paulc/c3zero-doorbell/src/ws2812_quad.rs

use anyhow::Result;
use esp_idf_hal::rmt::{config::TransmitConfig, FixedLengthSignal, PinState, Pulse, TxRmtDriver};
use std::time::Duration;

use crate::rgb::{Rgb, RgbLayout};

// ws2812 timings
const T0H: u64 = 400;
const T0L: u64 = 850;
const T1H: u64 = 800;
const T1L: u64 = 450;
const _RESET: u64 = 50000;

pub type Ws2812RmtChannel = esp_idf_hal::rmt::CHANNEL0;

// Quad WS2812 status display on RMT Channel 0
pub struct Ws2812RmtQuad<'a> {
    tx: TxRmtDriver<'a>,
    format: RgbLayout,
}

impl Ws2812RmtQuad<'_> {
    pub fn new(
        led: esp_idf_hal::gpio::AnyOutputPin,
        channel: Ws2812RmtChannel,
        format: RgbLayout,
    ) -> Result<Self> {
        let config = TransmitConfig::new().clock_divider(1);
        let tx = TxRmtDriver::new(channel, led, &config)?;
        Ok(Self { tx, format })
    }

    pub fn set(&mut self, leds: &[Rgb; 4]) -> Result<()> {
        let ticks_hz = self.tx.counter_clock()?;
        let (t0h, t0l, t1h, t1l) = (
            Pulse::new_with_duration(ticks_hz, PinState::High, &Duration::from_nanos(T0H))?,
            Pulse::new_with_duration(ticks_hz, PinState::Low, &Duration::from_nanos(T0L))?,
            Pulse::new_with_duration(ticks_hz, PinState::High, &Duration::from_nanos(T1H))?,
            Pulse::new_with_duration(ticks_hz, PinState::Low, &Duration::from_nanos(T1L))?,
        );
        let mut signal = FixedLengthSignal::<96>::new();
        for (n, led) in leds.iter().enumerate() {
            let colour: u32 = led.to_u32(self.format);
            for i in (0..24).rev() {
                if (colour >> i) & 1 == 0 {
                    signal.set((n * 24) + 23 - i, &(t0h, t0l))?;
                } else {
                    signal.set((n * 24) + 23 - i, &(t1h, t1l))?;
                }
            }
        }
        self.tx.start_blocking(&signal)?;
        Ok(())
    }
}
