paulc/c3zero-doorbell/examples/doorbell/main.rs

#![feature(lock_value_accessors)]

use esp_idf_hal::gpio::OutputPin;
use esp_idf_svc::eventloop::EspSystemEventLoop;
use esp_idf_svc::hal::prelude::*;
use esp_idf_svc::http::Method;
use esp_idf_svc::nvs::EspDefaultNvsPartition;
use esp_idf_svc::wifi::EspWifi;

use std::sync::{mpsc, Mutex};
use std::thread;
use std::time::Duration;

use doorbell::nvs::NVStore;
use doorbell::ota::Ota;
use doorbell::web::{BuildInfo, HomePage, NavBar, NavLink, WebServer};
use doorbell::wifi::{APConfig, APStore, WifiManager, WifiState};
use doorbell::ws2812::{colour, RgbLayout, Ws2812RmtSingle};

mod adc;
mod errlog;
mod led_task;
mod mqtt;
mod pushover;
mod watchdog;

const AP_SSID: &str = "ESP32C3-AP";
const AP_PASSWORD: &str = "password";

const NVS_NAMESPACE: &str = "DOORBELL";

const WATCHDOG_TIMEOUT: u64 = 60;

const BUILD_INFO: BuildInfo = BuildInfo {
    build_ts: env!("BUILD_TS"),
    build_branch: env!("BUILD_BRANCH"),
    build_hash: env!("BUILD_HASH"),
    build_profile: env!("BUILD_PROFILE"),
};

pub static WIFI_STATE: Mutex<WifiState> = Mutex::new(WifiState::NotConnected);

// Static NavBar
pub const NAVBAR: NavBar = NavBar {
    title: "Doorbell",
    links: &[
        NavLink {
            url: "/wifi",
            label: "Wifi",
        },
        NavLink {
            url: "/mqtt",
            label: "MQTT",
        },
        NavLink {
            url: "/pushover",
            label: "Pushover",
        },
        NavLink {
            url: "/ota_page",
            label: "OTA",
        },
        NavLink {
            url: "/adc",
            label: "ADC",
        },
        NavLink {
            url: "/reset_page",
            label: "Reset",
        },
    ],
};

fn main() -> anyhow::Result<()> {
    // It is necessary to call this function once. Otherwise some patches to the runtime
    // implemented by esp-idf-sys might not link properly. See https://github.com/esp-rs/esp-idf-template/issues/71
    esp_idf_svc::sys::link_patches();

    // Bind the log crate to the ESP Logging facilities
    esp_idf_svc::log::EspLogger::initialize_default();
    log::info!("Starting...");

    // Initialise peripherals
    let peripherals = Peripherals::take()?;
    let sys_loop = EspSystemEventLoop::take()?;
    let nvs_default_partition = EspDefaultNvsPartition::take()?;

    // Hardware Watchdog
    watchdog::init(peripherals.twdt, Duration::from_secs(WATCHDOG_TIMEOUT))?;

    // NVStore
    let nvs = NVStore::init(nvs_default_partition.clone(), NVS_NAMESPACE)?;

    // WiFi
    let mut wifi = WifiManager::new(EspWifi::new(
        peripherals.modem,
        sys_loop.clone(),
        Some(nvs_default_partition.clone()),
    )?)?;

    // Onboard WS2812 (GPIO10)
    let ws2812 = peripherals.pins.gpio10.downgrade_output();
    let channel = peripherals.rmt.channel0;
    let mut led = Ws2812RmtSingle::new(ws2812, channel, RgbLayout::Grb)?;
    led.set(colour::OFF)?;

    // LED task
    let (led_tx, led_rx) = mpsc::channel::<led_task::LedMessage>();
    let _led_task_id = thread::spawn(move || led_task::led_task(led, led_rx));

    // Start web server
    let mut web = WebServer::new(NAVBAR)?;

    // OTA
    let ota = Ota::new();

    // Add module handlers
    nvs.add_handlers(&mut web, NAVBAR)?;
    wifi.add_handlers(&mut web, NAVBAR)?;
    ota.add_handlers(&mut web, NAVBAR)?;

    // Home Page
    let home_page = HomePage::new(NAVBAR.title, BUILD_INFO.display_fields(), NAVBAR);
    home_page.set_status(WIFI_STATE.get_cloned()?.display_fields())?;
    web.add_handler("/", Method::Get, home_page.make_handler())?;

    // ADC Task
    let (adc_tx, adc_rx) = mpsc::channel();

    let _adc_task_id = adc::adc_task(
        peripherals.timer00,
        peripherals.adc1,
        peripherals.pins.gpio4,
        adc_tx,
    )?;

    web.add_handler("/adc/debug/on", Method::Get, adc::adc_debug_on_handler)?;
    web.add_handler("/adc/debug/off", Method::Get, adc::adc_debug_off_handler)?;
    web.add_handler("/adc/data", Method::Get, adc::adc_data)?;
    web.add_handler("/adc/set_params", Method::Post, adc::adc_set_params)?;
    web.add_handler("/adc", Method::Get, adc::make_adc_page(NAVBAR))?;

    // MQTT
    let mqtt_task = mqtt::MqttTask::new()?;
    mqtt_task.add_handlers(&mut web, NAVBAR)?;

    // Pushover
    let mut pushover = pushover::PushoverSender::new()?;
    pushover.add_handlers(&mut web, NAVBAR)?;

    // Start watchdog after initialisation
    watchdog::subscribe()?;
    let mut count = 0_usize;

    loop {
        let wifi_state = WIFI_STATE.get_cloned()?;
        let wifi_connected = wifi.is_connected()?;

        if !wifi_connected {
            log::info!("{wifi_state} :: {wifi_connected}");
        }

        match (&wifi_state, wifi_connected) {
            (WifiState::NotConnected, _) => {
                // NotConnected - try to connect to known AP (or start local AP)
                led_tx.send(led_task::LedMessage::Flash(colour::GREEN))?;
                wifi.scan()?;
                let wifi_state = wifi.try_connect(
                    &APStore::get_aps()?,
                    Some(APConfig::new(AP_SSID, AP_PASSWORD)?),
                    30_000,
                )?;
                log::info!("WifiState: {wifi_state:?}");

                // If we have connected start services
                if let WifiState::Station(_, _) = wifi_state {
                    // Start services
                    log::info!("Starting mqtt_task:");
                    mqtt_task.run()?;
                    mqtt_task.ring_msg(false)?;
                }

                // Update home page status
                home_page.set_status(wifi_state.display_fields())?;

                // Update WIFI_STATE
                WIFI_STATE.replace(wifi_state)?;

                // Update watchdog
                watchdog::feed()?;
            }
            (WifiState::Station(ref ap, _), false) => {
                log::error!("{count} :: {wifi_state} :: {wifi_connected}");
                // WiFi disconnected - try to reconnect (every 5 secs)
                if count.is_multiple_of(5) {
                    log::error!("WIFi Disconnected: Attempting to reconnect");
                    match wifi.connect_sta(ap, 30_000) {
                        Ok(WifiState::Station(config, ip_info)) => {
                            let wifi_state = WifiState::Station(config, ip_info);
                            log::info!("WIFi Reconnected: {wifi_state}");
                            // Update home page status
                            home_page.set_status(wifi_state.display_fields())?;
                            // Update WIFI_STATE
                            WIFI_STATE.replace(wifi_state)?;
                        }
                        Ok(_) => {
                            log::info!("WiFi Failed to Reconnect");
                        }
                        Err(e) => {
                            // Something went wrong - possibly reboot?
                            log::info!("WiFi Error Reconnecting: {e}");
                        }
                    }
                }

                // Flush adc_rx buffer
                while adc_rx.try_recv().is_ok() {}
                led_tx.send(led_task::LedMessage::Flash(colour::WHITE))?;
                thread::sleep(Duration::from_millis(1000));

                // We dont update watchdog here - timeout and reset if we dont re-connect
            }
            (WifiState::Station(_, _), true) => {
                // WiFi Online
                match adc_rx.recv_timeout(Duration::from_millis(1000)) {
                    Ok(msg) => match msg {
                        adc::RingMessage::RingStart(ref _s) => {
                            log::info!("adc_rx :: {msg:?}");
                            if let Err(e) = led_tx.send(led_task::LedMessage::Ring(true)) {
                                log::error!("LED Error: {e}");
                            }
                            if let Err(e) = mqtt_task.ring_msg(true) {
                                log::error!("MQTT Error: {e}");
                            }
                            if let Err(e) = mqtt_task.stats_msg() {
                                log::error!("MQTT Error: {e}");
                            }
                            if let Err(e) = pushover.send_ring_msg() {
                                log::error!("Pushover Error: {e}");
                            }
                        }
                        adc::RingMessage::RingStop => {
                            log::info!("adc_rx :: {msg:?}");
                            if let Err(e) = led_tx.send(led_task::LedMessage::Ring(false)) {
                                log::error!("LED Error: {e}");
                            }
                            if let Err(e) = mqtt_task.ring_msg(false) {
                                log::error!("MQTT Error: {e}");
                            }
                        }
                    },
                    Err(mpsc::RecvTimeoutError::Timeout) => {}
                    Err(e) => log::error!("ERROR :: adc_rx :: {e}"),
                }
                led_tx.send(led_task::LedMessage::Flash(colour::BLUE))?;

                // Update watchdog
                watchdog::feed()?;
            }
            (WifiState::AP(_, _), _) => {
                // AP Mode
                // Flush adc_rx buffer
                while adc_rx.try_recv().is_ok() {}
                thread::sleep(Duration::from_millis(1000));
                led_tx.send(led_task::LedMessage::Flash(colour::GREEN))?;

                // Update watchdog
                watchdog::feed()?;
            }
        }

        // Update counter
        count += 1;
    }
}
